particle-iot/photon/eagle/photon_v010/photon_at7020_2/photon_at7020_2_rf_nets.pdf

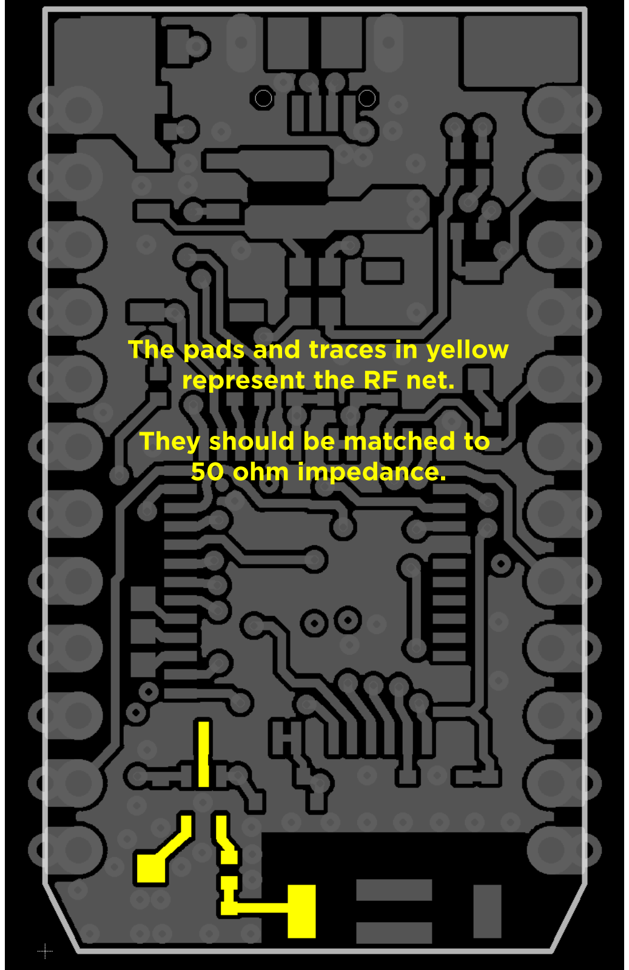
[picture p3: page 1]
